LennartKlaver/TelescopeTracker/Camera mount/view1.PNG

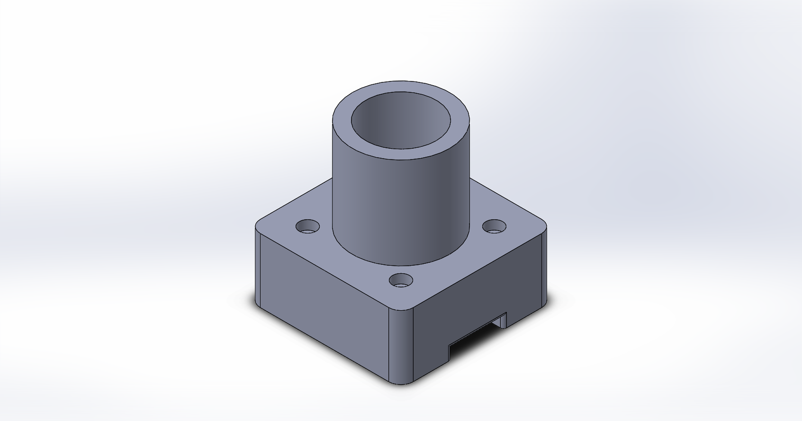
Camera mount/view1.PNG
