LennartKlaver/TelescopeTracker/Camera mount/view2.PNG

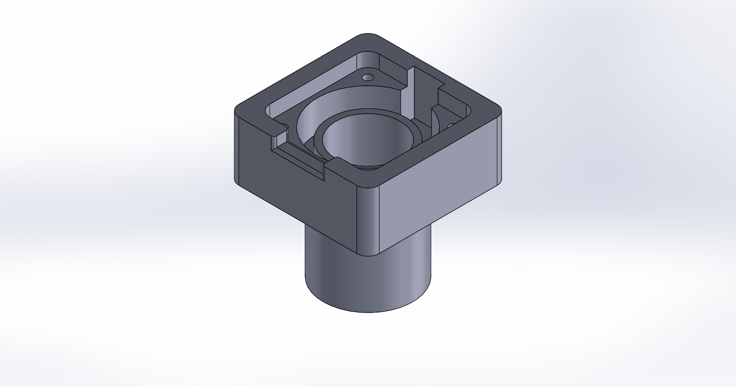
Camera mount/view2.PNG
