LennartKlaver/TelescopeTracker/Assembly/IMG_0387.jpg

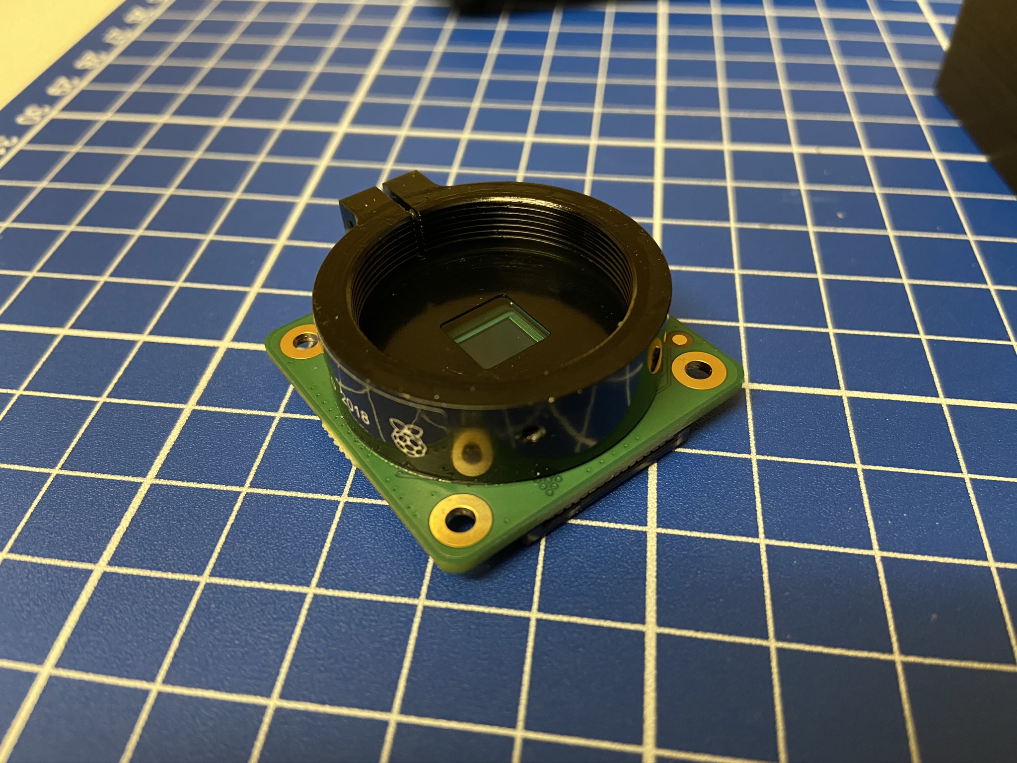
Assembly/IMG_0387.jpg
