LennartKlaver/TelescopeTracker/Assembly/IMG_0389.jpg

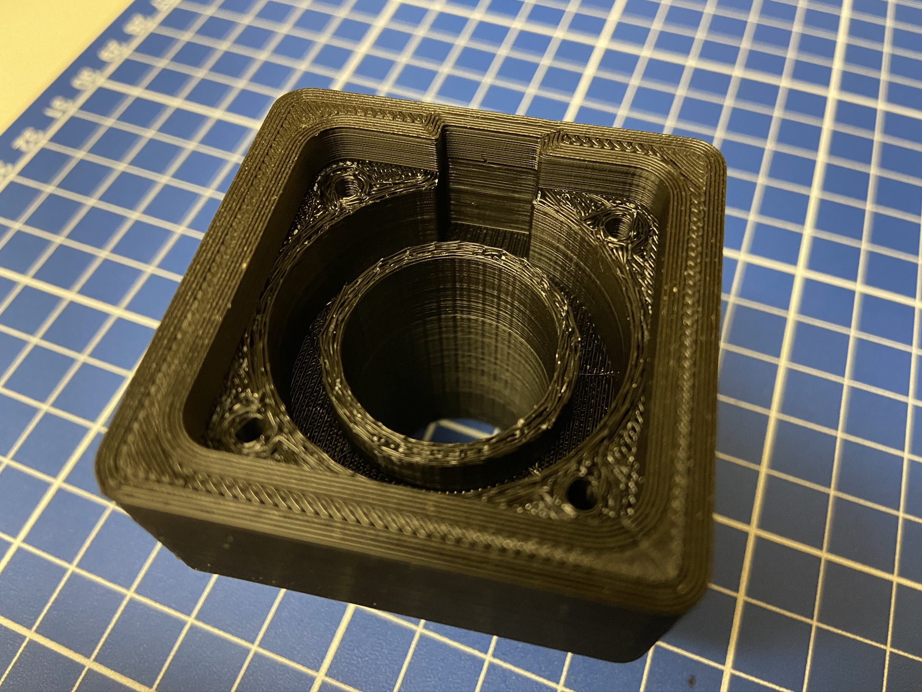
Assembly/IMG_0389.jpg
