LennartKlaver/TelescopeTracker/Assembly/IMG_0391.jpg

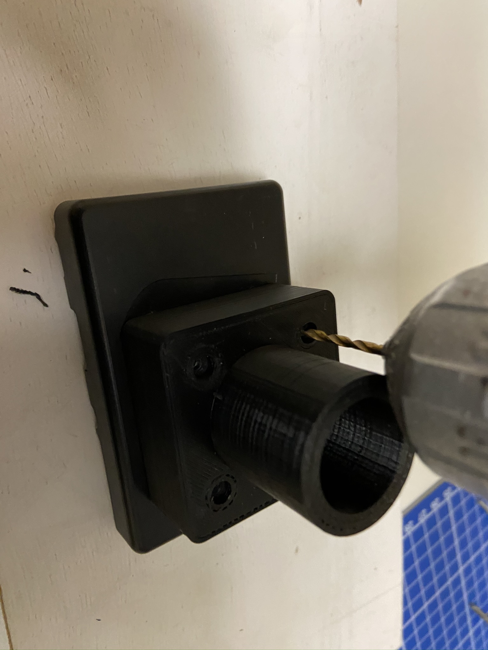
Assembly/IMG_0391.jpg
