LennartKlaver/TelescopeTracker/Assembly/IMG_0392.jpg

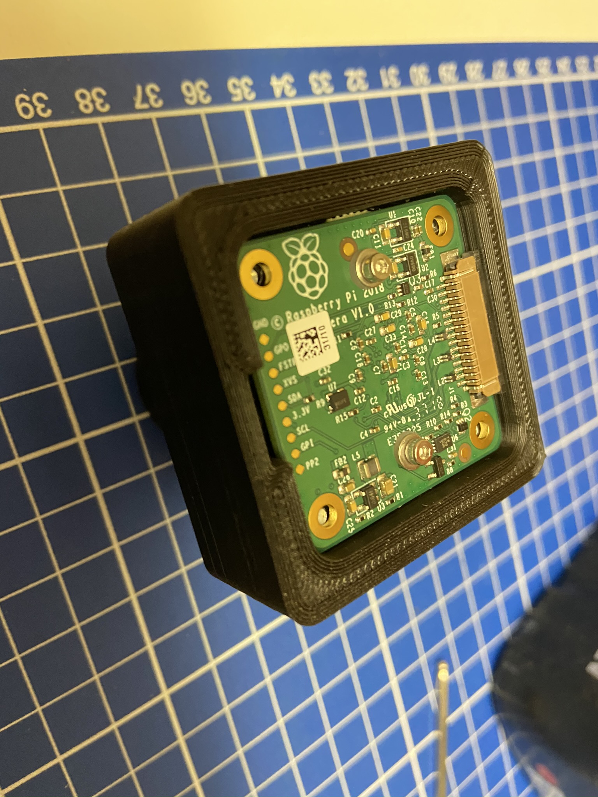
Assembly/IMG_0392.jpg
