LennartKlaver/TelescopeTracker/Assembly/IMG_0394.jpg

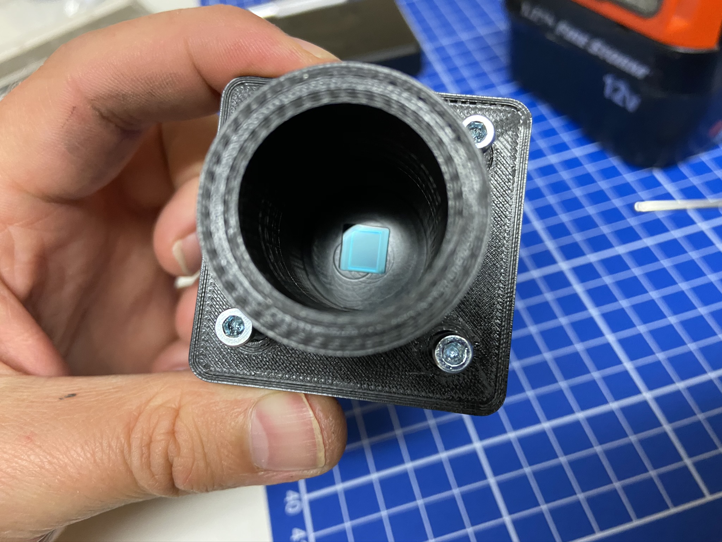
Assembly/IMG_0394.jpg
