LennartKlaver/TelescopeTracker/Assembly/IMG_0398.jpg

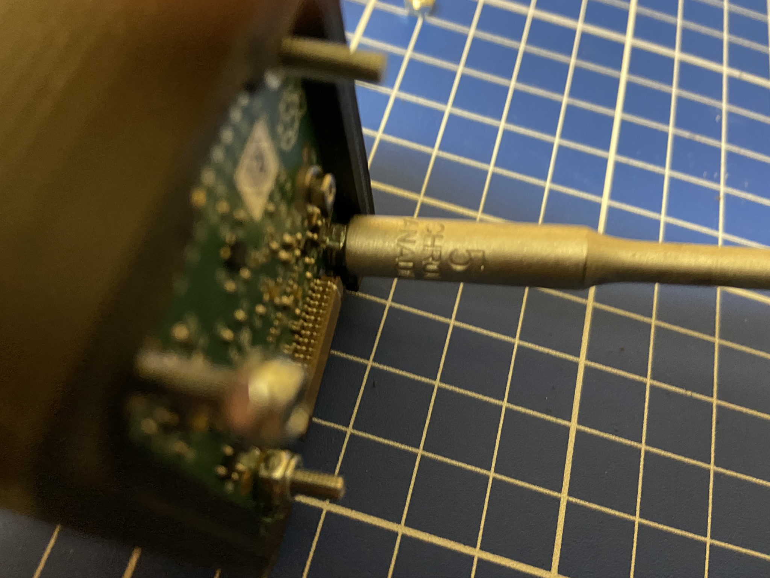
Assembly/IMG_0398.jpg
