LennartKlaver/TelescopeTracker/Assembly/IMG_0399.jpg

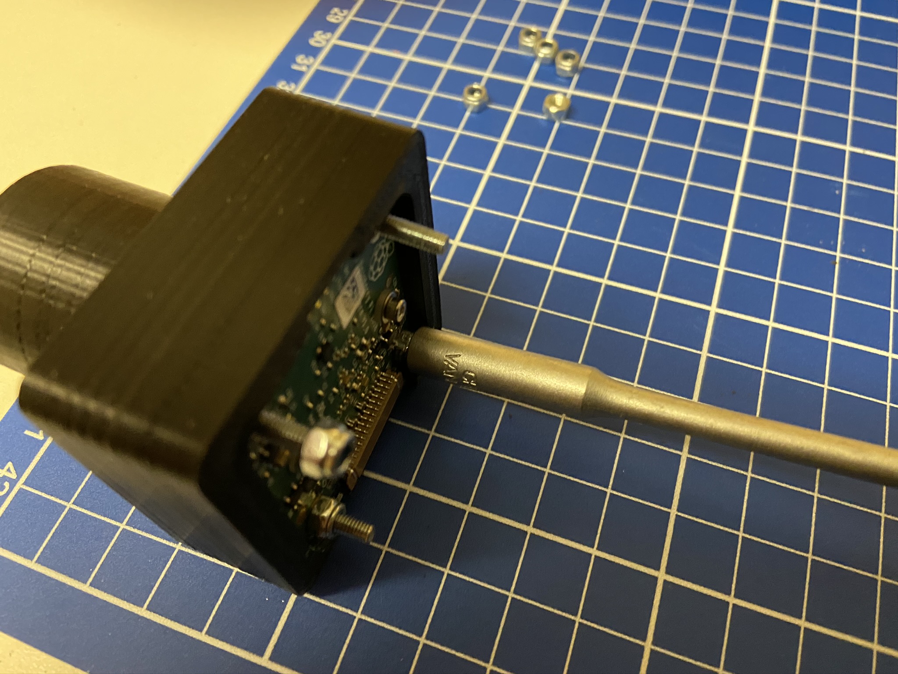
Assembly/IMG_0399.jpg
