LennartKlaver/TelescopeTracker/Assembly/IMG_0401.jpg

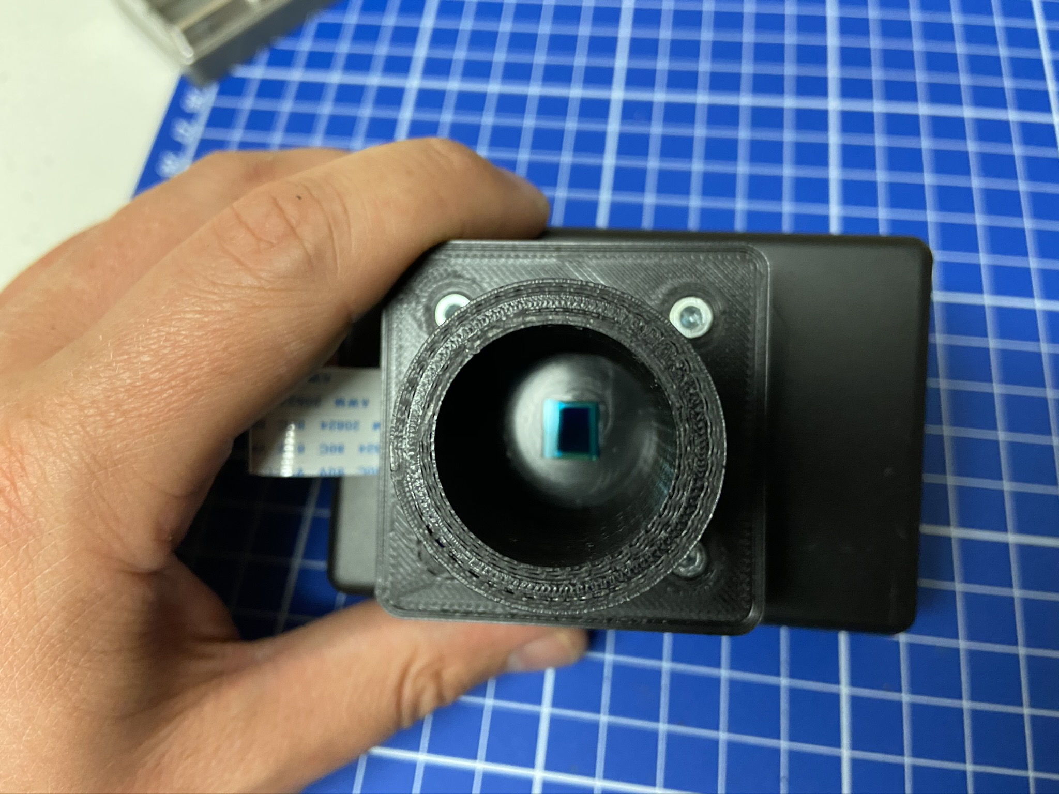
Assembly/IMG_0401.jpg
