LennartKlaver/TelescopeTracker/Assembly/IMG_0402.jpg

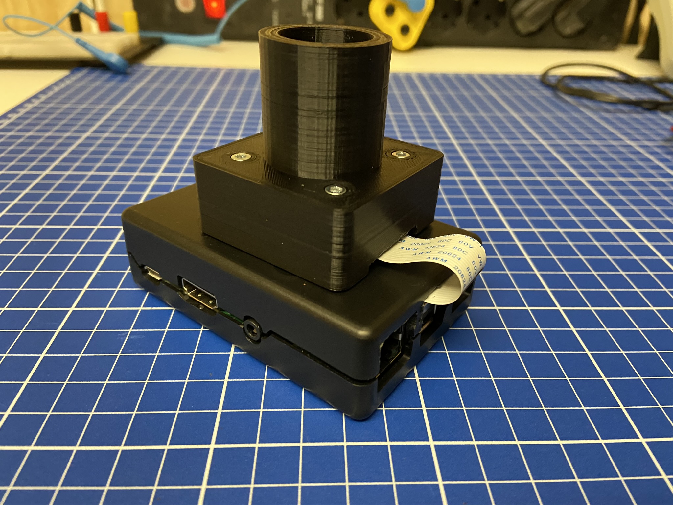
Assembly/IMG_0402.jpg
