LennartKlaver/TelescopeTracker/Assembly/IMG_0403.jpg

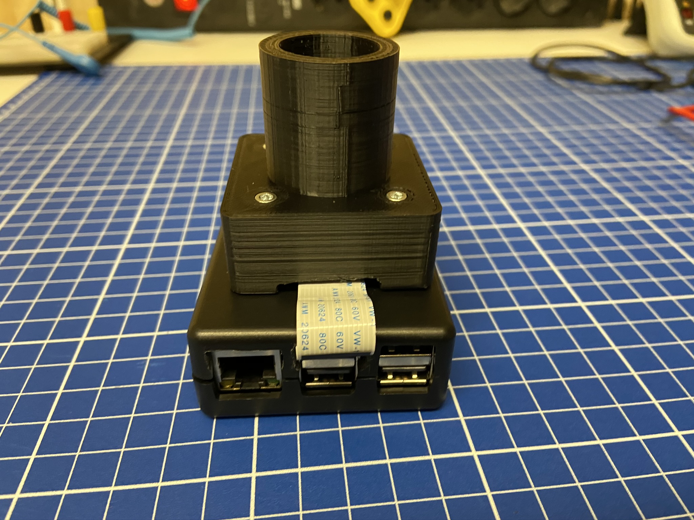
Assembly/IMG_0403.jpg
