LennartKlaver/TelescopeTracker/Assembly/IMG_0405.jpg

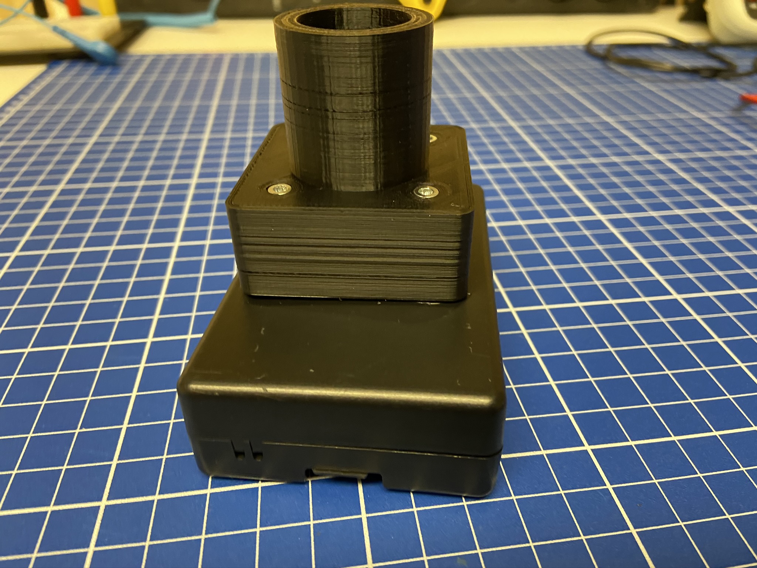
Assembly/IMG_0405.jpg
