LennartKlaver/TelescopeTracker/Assembly/IMG_0426.jpg

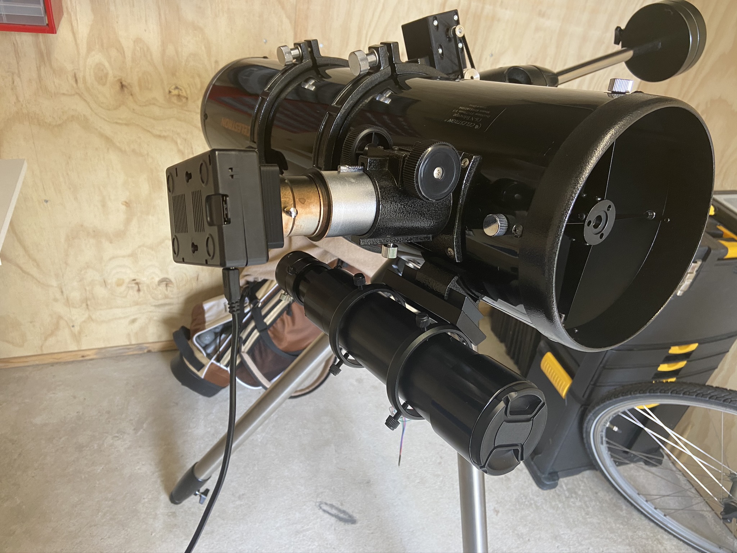
Assembly/IMG_0426.jpg
